0x007E/gap/firmware/GAP_GAME/main.h

#ifndef MAIN_H_
#define MAIN_H_

	#define F_CPU 20000000UL

	#include <avr/io.h>
	#include <util/delay.h>

	#include "../lib/hal/avr0/system/system.h"
	#include "../lib/hal/avr0/control/control.h"
	#include "../lib/hal/avr0/uart/uart.h"
	#include "../lib/matrix/matrix.h"

#endif /* MAIN_H_ */
